ZakKemble/NWatch/wiki/breakout.png

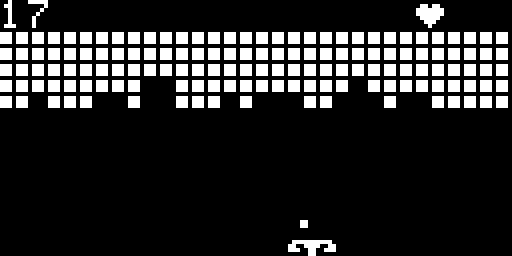
wiki/breakout.png
