ZakKemble/NWatch/wiki/cardodge.png

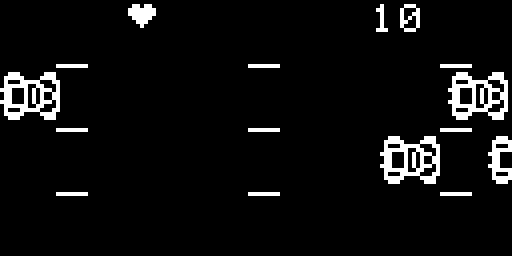
wiki/cardodge.png
