ZakKemble/NWatch/wiki/diag.png

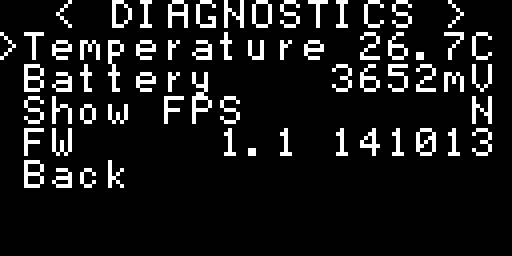
wiki/diag.png
