ZakKemble/NWatch/wiki/mainscreen.png

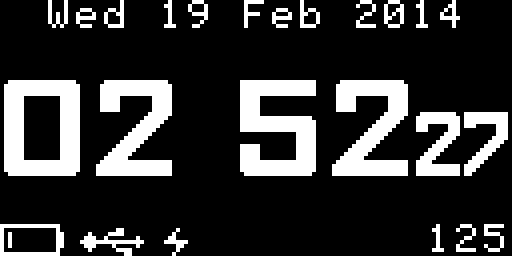
wiki/mainscreen.png
