ZakKemble/NWatch/wiki/stopwatch.png

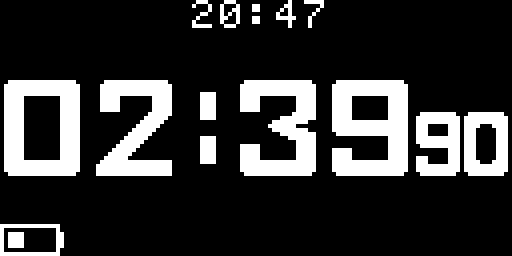
wiki/stopwatch.png
