ZakKemble/NWatch/firmware/src/watch/resources.c

/*
 * Project: N|Watch
 * Author: Zak Kemble, contact@zakkemble.co.uk
 * Copyright: (C) 2013 by Zak Kemble
 * License: GNU GPL v3 (see License.txt)
 * Web: http://blog.zakkemble.co.uk/diy-digital-wristwatch/
 */

#include "common.h"

const char dowChars[] PROGMEM = STR_DOWCHARS;

const char days[7][BUFFSIZE_STR_DAYS] PROGMEM = {
	STR_MON,
	STR_TUE,
	STR_WED,
	STR_THU,
	STR_FRI,
	STR_SAT,
	STR_SUN
};

const char months[12][BUFFSIZE_STR_MONTHS] PROGMEM = {
	STR_JAN,
	STR_FEB,
	STR_MAR,
	STR_APR,
	STR_MAY,
	STR_JUN,
	STR_JUL,
	STR_AUG,
	STR_SEP,
	STR_OCT,
	STR_NOV,
	STR_DEC
};

const byte livesImg[] PROGMEM ={
	0x06,0x0F,0x1F,0x3E,0x1F,0x0F,0x06,
};

const byte stopwatch[] PROGMEM ={
	0x3C,0x42,0x81,0x9D,0xA1,0x81,0x42,0x3C,
};

const byte dowImg[7][8] PROGMEM ={
	{DOWIMG_MON},
	{DOWIMG_TUE},
	{DOWIMG_WED},
	{DOWIMG_THU},
	{DOWIMG_FRI},
	{DOWIMG_SAT},
	{DOWIMG_SUN},
};

const byte menu_default[] PROGMEM ={
	0x00,0x00,0x00,0x00,0x00,0x80,0xE0,0xF0,0xF8,0xFC,0xFC,0xFC,0x3E,0x1E,0x1E,0x1E,0x1E,0x1E,0x3E,0x7C,0xFC,0xFC,0xF8,0xF0,0xE0,0x80,0x00,0x00,0x00,0x00,0x00,0x00,
	0x00,0x00,0x00,0x00,0x00,0x01,0x01,0x01,0x01,0x01,0x01,0x00,0x00,0x00,0x00,0x80,0xC0,0xE0,0xF0,0xF8,0xFF,0xFF,0xFF,0x7F,0x3F,0x0F,0x00,0x00,0x00,0x00,0x00,0x00,
	0x00,0x00,0x00,0x00,0x00,0x00,0x00,0x00,0x00,0x00,0x00,0x00,0x7C,0x7E,0x7F,0x7F,0x7F,0x7F,0x0F,0x03,0x01,0x01,0x00,0x00,0x00,0x00,0x00,0x00,0x00,0x00,0x00,0x00,
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
//		0x00, 0x00, 0x00, 0x00, 0x00, 0x01, 0x01, 0x01, 0x01, 0x01, 0x00, 0x00, 0x00, 0x00, 0x00, 0x00,
//		0x00, 0x00, 0x00, 0x00, 0x00, 0x3F, 0x3F, 0x3F, 0x3F, 0x3F, 0x00, 0x00, 0x00, 0x00, 0x00, 0x00
//	},
};
*/
