ZakKemble/NWatch/firmware/src/watch/includes/devices/led.h

/*
 * Project: N|Watch
 * Author: Zak Kemble, contact@zakkemble.co.uk
 * Copyright: (C) 2013 by Zak Kemble
 * License: GNU GPL v3 (see License.txt)
 * Web: http://blog.zakkemble.co.uk/diy-digital-wristwatch/
 */

#ifndef LED_H_
#define LED_H_

typedef enum
{
	LED_RED,
	LED_GREEN
} led_t;

//#define LED_FLASH_INFINITE	0
//#define LED_ALL				255
#define LED_FLASH_FAST	50
#define LED_BRIGHTNESS_MAX	255

void led_init(void);
void led_flash(led_t, byte, byte);
BOOL led_flashing(void);
void led_update(void);
void led_stop(void);

#endif /* LED_H_ */
