ZakKemble/NWatch/firmware/src/watch/includes/devices/ds3231_defs.h

/*
 * Project: N|Watch
 * Author: Zak Kemble, contact@zakkemble.co.uk
 * Copyright: (C) 2013 by Zak Kemble
 * License: GNU GPL v3 (see License.txt)
 * Web: http://blog.zakkemble.co.uk/diy-digital-wristwatch/
 */

#ifndef DS3231_DEFS_H_
#define DS3231_DEFS_H_

// I2C addresses
#define DS3231_I2C		0b11010000

// Control register settings
#define DS3231_BIT_EOSC		7
#define DS3231_BIT_1HZ		6
#define DS3231_BIT_CONV		5
#define DS3231_BIT_RS1		4
#define DS3231_BIT_RS2		3
#define DS3231_BIT_INTCN	2
#define DS3231_BIT_A2IE		1
#define DS3231_BIT_A1IE		0

// Status register settings
#define DS3231_BIT_EN32KHZ	3
#define DS3231_BIT_A2F		1
#define DS3231_BIT_A1F		0

// Time registers
#define DS3231_ADDR_SECS	0x00
#define DS3231_ADDR_MINS	0x01
#define DS3231_ADDR_HRS		0x02
#define DS3231_ADDR_DAY		0x03
#define DS3231_ADDR_DATE	0x04
#define DS3231_ADDR_MONTH	0x05
#define DS3231_ADDR_YEAR	0x06

// Alarm 1 registers
#define DS3231_ADDR_ALARM1_SECS		0x07
#define DS3231_ADDR_ALARM1_MINS		0x08
#define DS3231_ADDR_ALARM1_HRS		0x09
#define DS3231_ADDR_ALARM1_DAYDATE	0x0A

// Alarm 2 registers
#define DS3231_ADDR_ALARM2_MINS		0x0B
#define DS3231_ADDR_ALARM2_HRS		0x0C
#define DS3231_ADDR_ALARM2_DAYDATE	0x0D

// Other registers
#define DS3231_ADDR_CTRL	0x0E
#define DS3231_ADDR_STATUS	0x0F
#define DS3231_ADDR_AGING	0x10
#define DS3231_ADDR_TEMPH	0x11
#define DS3231_ADDR_TEMPL	0x12

#endif /* DS3231_DEFS_H_ */
